bazsimarkus/rtty-transmitter/ltspice/Cascode-AM-modulator.asc

C1: cap; 100p; V=100
C2: cap; 100n
C3: cap; 10µ; V=100
C4: cap; 1n; V=100
L1: ind; 1m; Rser=1m
L2: ind; 330µ; Rser=1m
Q1: npn; 2N2222
Q2: npn; 2N2222
R1: res; 22k; tol=1 pwr=1
R2: res; 10k; tol=1 pwr=1
R3: res; 470; tol=1 pwr=1
R4: res; 220; tol=1 pwr=1
R5: res; 5k; tol=1 pwr=10
R6: res; 100; tol=1 pwr=10
V1: voltage; SINE(2.5 1 720k)
V3: voltage; 5
V4: voltage; SINE(2.5 0.5 1000)
Named nets: 0
.tran .005
